cyborg5/Ultimate-Remote/ultimate_remote/sa_cable_codes.h

/*
 * Codes for my Scientific Atlantic cable box which uses PANASONIC_OLD but I abbreviate it "SA"
 */
#define	SA_0	0x373119   
#define	SA_1	0x36113d   
#define	SA_2	0x37111d   
#define	SA_3	0x36912d   
#define	SA_4	0x37910d   
#define	SA_5	0x365135   
#define	SA_6	0x375115   
#define	SA_7	0x36d125   
#define	SA_8	0x37d105   
#define	SA_9	0x363139   
#define	SA_A	0x37e902   
#define	SA_B	0x36193c   
#define	SA_C	0x37191c   
#define	SA_CHDN	0x36f121   
#define	SA_CHUP	0x377111   
#define	SA_D	0xf7e10
#define	SA_DOWN	0x37a10b   
#define	SA_EXIT	0x366932   //also labeled return
#define	SA_FAV	0x37f101   
#define	SA_FF	0x36293a   
#define	SA_GUIDE	0x36c127   
#define	SA_HASH_ASPECT	0x36b928   //also labeled number input
#define	SA_HDOD	0x36d125  //same as “7”
#define	SA_INFO	0x36213b   
#define	SA_LEFT	0x37810f   
#define	SA_LIST	0x36c926   //also labeled menu
#define	SA_LIVE	0x36b129   //also labeled “D”
#define	SA_M2	0xf3e18
#define	SA_MUTE	0x36829e   
#define	SA_NEXT_DAY	0xfe603   
#define	SA_ON_DEMAND	0x37d105 //same as “8”?
#define	SA_OPTIONS	0x373918   
#define	SA_PAGE_DOWN	0x37d904   
#define	SA_PAGE_UP	0x36d924   
#define	SA_PAUSE	0x374117   
#define	SA_PIP_CHDN	0x37f900   
#define	SA_PIP_CHUP	0x36e922   
#define	SA_PIP_MOVE	0x377910   //also labeled next
#define	SA_PIP_SWAP	0x367930   //also labeled end
#define	SA_PIP_TGL	0x37b908 //also labeled Start
#define	SA_PLAY	0x37990c   
#define	SA_POWER	0x37c107   
#define	SA_PREV	0x37c906   
#define	SA_PREV_DAY	0xe163d   
#define	SA_RECALL	0x36e123   //also labeled last
#define	SA_RECORD	0x375914   
#define	SA_REWIND	0x37291a   
#define	SA_RIGHT	0x364137   
#define	SA_SELECT	0x366133   
#define	SA_SHIFT	0xff601
#define	SA_SOURCE	0x376113   //also labeled input
#define	SA_STAR	0x37e103   
#define	SA_STOP	0x365934   
#define	SA_UP	0x36812f   
#define	SA_VOLUME_DOWN	0x37091e   
#define	SA_VOLUME_UP	0x36093e   
