cyborg5/Ultimate-Remote/ultimate_remote/samsung_bluray_codes.h

/*
 *  Codes for my Samsung 3D Blu-ray player that uses SAMSUNG36 36 bit protocol. The address portion is always 0x400 and the code handles it. 
 * 
 */
#define BR_0	0xED02F
#define BR_1	0xE40BF
#define BR_2	0xEC03F
#define BR_3	0xE20DF
#define BR_4	0xEA05F
#define BR_5	0xE609F
#define BR_6	0xEE01F
#define BR_7	0xE10EF
#define BR_8	0xE906F
#define BR_9	0xE50AF
#define BR_A	0xE847B
#define BR_AUDIO	0xEA45B
#define BR_B	0xE44BB
#define BR_BONUS_VIEW	0xECC33
#define BR_C	0xEC43B
#define BR_D	0xE24DB
#define BR_DISK_MENU	0xEB847
#define BR_DOWN	0xE9867
#define BR_EJECT	0xE807F
#define BR_EXIT	0xED42B
#define BR_FF	0xEA857
#define BR_FULL_SCREEN	0xE9C63
#define BR_INFO	0xE7887
#define BR_INTERNET	0xE1CE3
#define BR_LEFT	0xED827
#define BR_MENU	0xE6897
#define BR_NEXT_CHAP	0xE8877
#define BR_PAUSE	0xE4CB3
#define BR_PLAY	0xE28D7
#define BR_POWER	0xE00FF
#define BR_PREV_CHAP	0xEB04F
#define BR_REPEAT	0xEE41B
#define BR_RETURN	0xEE817
#define BR_REW	0xE48B7
#define BR_RIGHT	0xE58A7
#define BR_SELECT	0xE38C7
#define BR_STOP	0xEC837
#define BR_SUBTITLE	0xE649B
#define BR_TITLE_MENU	0xE04FB
#define BR_TOOLS	0xE5CA3
#define BR_UP	0xE18E7
