cyborg5/Ultimate-Remote/ultimate_remote/samsung_necx_codes.h

/*
 *  Codes for my Samsung TVs which use NECX protocol
 */
#define TV_POWER	0xe0e040bf
#define TV_INPUT	0xe0e0807f //labeled as "source"
#define TV_CH_UP	0xE0E048b7
#define TV_CH_DN	0xE0E008f7
#define TV_VOLUP  0xe0e0e01f
#define TV_VOLDN  0xe0e0d02f
#define TV_MUTE    0xe0e0f00f
#define TV_INFO	0xe0e0f807
#define TV_ZOOM	0xe0e07c83 //label says "p.Size"
#define TV_CC	0xE0E0A45b

#define TV_MENU	0xe0e058a7
#define TV_TOOLS	0xe0e0d22d
#define TV_LEFT 0xE0E0A659
#define TV_RIGHT 0xE0E046B9
#define TV_UP 0xE0E006F9
#define TV_DOWN 0xE0E08679
#define TV_SELECT 0xE0E016E9
#define TV_EXIT	0xE0E0B44b
#define TV_RETURN	0xE0E01ae5
#define TV_3D	0xe0e0f906

#define TV_REW	0xE0E0A25d
#define TV_PLAY	0xE0E0E21d
#define TV_FF	0xE0E012ed
#define TV_PAUSE	0xE0E052ad
#define TV_STOP	0xE0E0629d
#define TV_A	0xE0E036c9
#define TV_B	0xE0E028d7
#define TV_C	0xE0E0A857
#define TV_D	0xE0E06897
#define TV_MEDIAP	0xE0E031ce

#define TV_CONTENT	0xE0E09e61
#define TV_ITV	0xE0E0C936
#define TV_YAHOO	0xE0E0Ca35
#define TV_PREV	0xE0E0C837
#define TV_FAV	0xE0E022dd
#define TV_CH_LIST	0xE0E0D629

#define TV_1	0xE0E020df
#define TV_2	0xE0E0A05f
#define TV_3	0xE0E0609f
#define TV_4	0xE0E010ef
#define TV_5	0xE0E0906f
#define TV_6	0xE0E050af
#define TV_7	0xE0E030cf
#define TV_8	0xE0E0B04f
#define TV_9	0xE0E0708f
#define TV_MINUS	0xE0E0C43b
#define TV_0	0xE0E08877

#define TV_REC	0xE0E0926d
