cyborg5/Ultimate-Remote/ultimate_remote/sony_amp_codes.h

/*
 * Sony surroundsound amplifier
 */
#define AMP_AFD_2CH	0x710d	// 
#define AMP_AM	0x2c0c	// 
#define AMP_MENU	0x770d	// Menu
#define AMP_BD_DVD	0x68114	// 
#define AMP_DISPLAY	0x690c	// 
#define AMP_DOWN	0x4f0d	// Down Arrow
#define AMP_FF	0xBc110	// 
#define AMP_FM	0xC0c	// 
#define AMP_GAME	0x1f0c	// 
#define AMP_HOME	0x650c	// Info
#define AMP_IPHONE	0x4e110	// 
#define AMP_LEFT	0x2f0d	// Left Arrow
#define AMP_MOVIE	0x610d	// 
#define AMP_MUSIC	0x490d	// 7 
#define AMP_MUTE	0x140c	// Mute
#define AMP_OPTIONS	0xCe110	// 
#define AMP_PLAY_PAUSE	0x5c110	// 
#define AMP_POWER	0x540c	// Power
#define AMP_REPEAT	0x34110	// 
#define AMP_RETURN	0xBe110	// 
#define AMP_REWIND	0xC110	// (20 bits)
#define AMP_RIGHT	0x6f0d	// Right Arrow
#define AMP_SACD_CD	0x520c	// 3
#define AMP_SAT_CATV	0x600d	// 
#define AMP_SELECT	0x180c	// Select
#define AMP_SHUFFLE 	0x54110	// 
#define AMP_SLEEP	0x30c	// Sleep
#define AMP_STOP	0x1c110	// 
#define AMP_TV	0x2b0c	// 6
#define AMP_UP	0xF0d	// Up Arrow
#define AMP_USB	0xE8114	// 
#define AMP_VIDEO	0x220c	// 4
#define AMP_VOL_DN	0x640c	// Vol-
#define AMP_VOL_UP	0x240c	// Vol+
